Wisoxx/adjustable-power-supply/adjustable_power_supply_schematic/adjustable_power_supply.kicad_pcb

## KiCad design circuit-schematics/Receiver+transmitter/receiver.kicad_sch

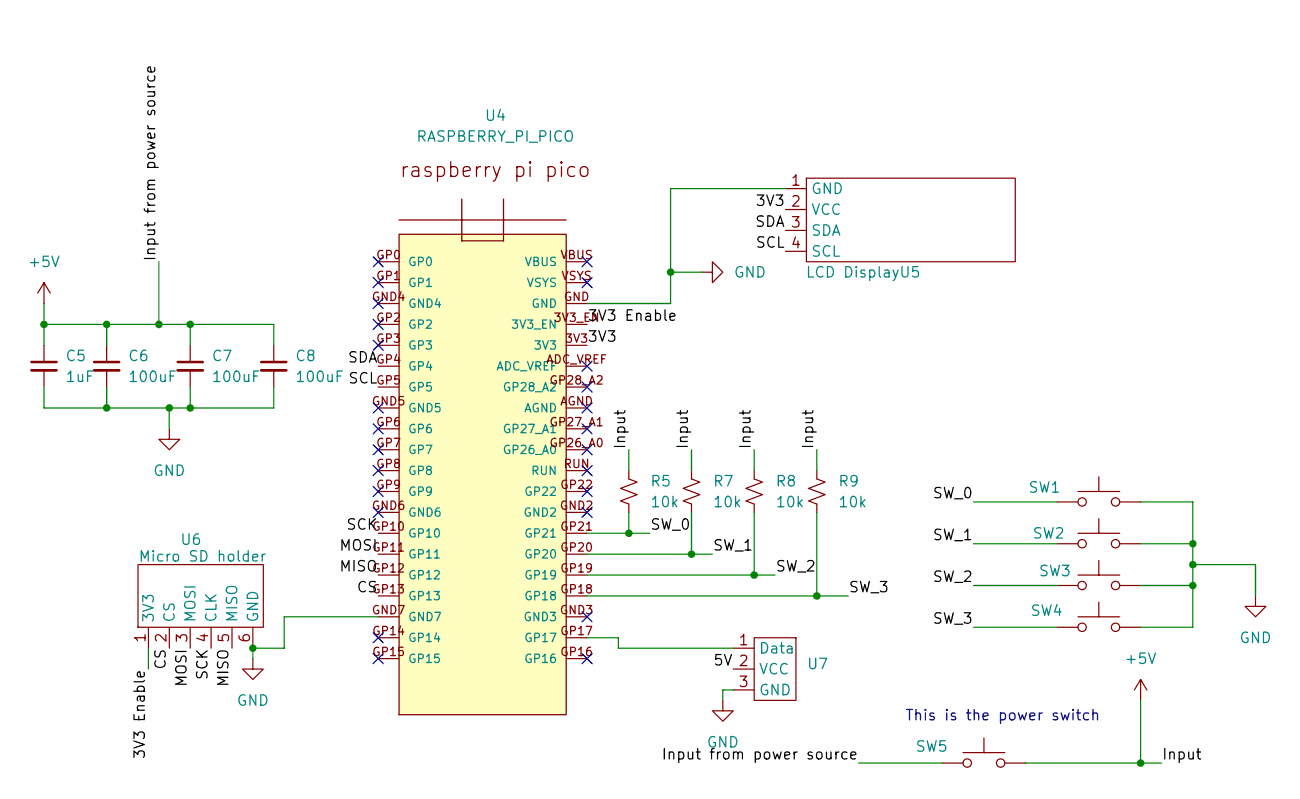
[picture p7: schematic receiver.kicad_sch]

Parts:
C5: 1uF
C6, C7, C8: 100uF
R5, R7, R8, R9: 10k
SW1, SW2, SW3, SW4, SW5: SW_Push
U4: RASPBERRY_PI_PICO
U5: LCD Display
U6: Micro SD holder
U7: (no value)

Connections:
3V3: U4.3V3, U5.2 (VCC)
3V3 Enable: U4.3V3_EN, U6.1 (3V3)
5V: U7.2 (VCC)
+5V: C5.1, C6.1, C7.1, C8.1, R5.1, R7.1, R8.1, R9.1, SW5.1, SW5.2
CS: U4.GP13, U6.2 (CS)
GND: C5.2, C6.2, C7.2, C8.2, SW1.2, SW2.2, SW3.2, SW4.2, U4.GND, U4.GND7, U5.1 (GND), U6.6 (GND), U7.3 (GND)
MISO: U4.GP12, U6.5 (MISO)
MOSI: U4.GP11, U6.3 (MOSI)
unnamed: U4.GP17, U7.1 (Data)
SCK: U4.GP10, U6.4 (CLK)
SCL: U4.GP5, U5.4 (SCL)
SDA: U4.GP4, U5.3 (SDA)
SW_0: R5.2, SW1.1, U4.GP21
SW_1: R7.2, SW2.1, U4.GP20
SW_2: R8.2, SW3.1, U4.GP19
SW_3: R9.2, SW4.1, U4.GP18

Notes on the sheet:
This is the power switch
