Wisoxx/adjustable-power-supply/adjustable_power_supply_schematic/adjustable_power_supply.kicad_pcb

## KiCad design circuit-schematics/Receiver+transmitter/transmitter.kicad_sch

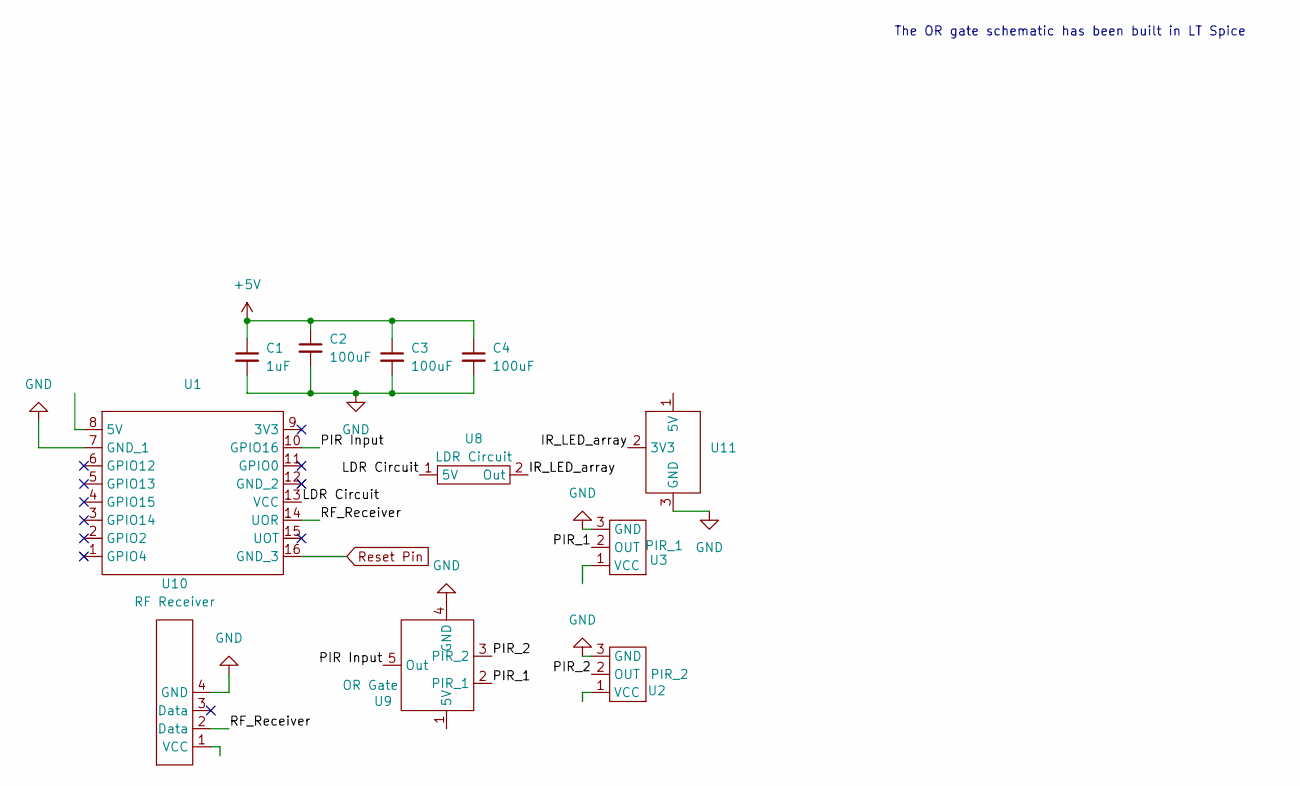
[picture p8: schematic transmitter.kicad_sch]

Parts:
C1: 1uF
C2, C3, C4: 100uF
U1, U11: (no value)
U2: PIR_2
U3: PIR_1
U8: LDR Circuit
U9: OR Gate
U10: RF Receiver

Connections:
+5V: C1.1, C2.1, C3.1, C4.1
GND: C1.2, C2.2, C3.2, C4.2, U1.7 (GND_1), U2.3 (GND), U3.3 (GND), U9.4 (GND), U10.4 (GND), U11.3 (GND)
IR_LED_array: U8.2 (Out), U11.2 (3V3)
LDR Circuit: U1.13 (VCC), U8.1 (5V)
PIR Input: U1.10 (GPIO16), U9.5 (Out)
PIR_1: U3.2 (OUT), U9.2 (PIR_1)
PIR_2: U2.2 (OUT), U9.3 (PIR_2)
RF_Receiver: U1.14 (UOR), U10.2 (Data)
Reset Pin: U1.16 (GND_3)

Notes on the sheet:
The OR gate schematic has been built in LT Spice
